hagen-gloetter/ESP32-LED-Strips-Control/code_v1_production/boot.py

# This file is executed on every boot (including wake-boot from deepsleep)
import esp
#esp.osdebug(None)
from machine import Pin
#esp.osdebug(None)
import gc
import time
import webrepl
#import webrepl_setup
print ("boot.py")

webrepl.start()
#print ("boot.py done")

import os
import machine

print ("boot.py get_wifi_connection")
import class_wifi_connection
wifi=None
#get_wifi_connection.connect()
class_wifi_connection.WifiConnect()
print ("boot.py done")
